Frol00/Mirage-3D-Scanning-System/software/data_processing_node/MirageApp/source/InfiniTAM-master/InfiniTAM/Apps/InfiniTAM/InfiniTAM.cpp

// Copyright 2014-2017 Oxford University Innovation Limited and the authors of InfiniTAM

#include <cstdlib>
#include <iostream>
#include <stdexcept>

#include "UIEngine.h"

#include "../../InputSource/OpenNIEngine.h"
#include "../../InputSource/Kinect2Engine.h"
#include "../../InputSource/LibUVCEngine.h"
#include "../../InputSource/PicoFlexxEngine.h"
#include "../../InputSource/RealSenseEngine.h"
#include "../../InputSource/LibUVCEngine.h"
#include "../../InputSource/RealSense2Engine.h"
#include "../../InputSource/FFMPEGReader.h"
#include "../../ITMLib/ITMLibDefines.h"
#include "../../ITMLib/Core/ITMBasicEngine.h"
#include "../../ITMLib/Core/ITMBasicSurfelEngine.h"
#include "../../ITMLib/Core/ITMMultiEngine.h"

using namespace InfiniTAM::Engine;
using namespace InputSource;
using namespace ITMLib;

/** Create a default source of depth images from a list of command line
    arguments. Typically, @para arg1 would identify the calibration file to
    use, @para arg2 the colour images, @para arg3 the depth images and
    @para arg4 the IMU images. If images are omitted, some live sources will
    be tried.
*/
static void CreateDefaultImageSource(ImageSourceEngine* & imageSource, IMUSourceEngine* & imuSource, const char *arg1, const char *arg2, const char *arg3, const char *arg4)
{
	const char *calibFile = arg1;
	const char *filename1 = arg2;
	const char *filename2 = arg3;
	const char *filename_imu = arg4;

	if (strcmp(calibFile, "viewer") == 0)
	{
		imageSource = new BlankImageGenerator("", Vector2i(640, 480));
		printf("starting in viewer mode: make sure to press n first to initiliase the views ... \n");
		return;
	}

	printf("using calibration file: %s\n", calibFile);

	if ((imageSource == NULL) && (filename2 != NULL))
	{
		printf("using rgb images: %s\nusing depth images: %s\n", filename1, filename2);
		if (filename_imu == NULL)
		{
			ImageMaskPathGenerator pathGenerator(filename1, filename2);
			imageSource = new ImageFileReader<ImageMaskPathGenerator>(calibFile, pathGenerator);
		}
		else
		{
			printf("using imu data: %s\n", filename_imu);
			imageSource = new RawFileReader(calibFile, filename1, filename2, Vector2i(320, 240), 0.5f);
			imuSource = new IMUSourceEngine(filename_imu);
		}

		if (imageSource->getDepthImageSize().x == 0)
		{
			delete imageSource;
			if (imuSource != NULL) delete imuSource;
			imuSource = NULL;
			imageSource = NULL;
		}
	}

	if ((imageSource == NULL) && (filename1 != NULL) && (filename_imu == NULL))
	{
		imageSource = new InputSource::FFMPEGReader(calibFile, filename1, filename2);
		if (imageSource->getDepthImageSize().x == 0)
		{
			delete imageSource;
			imageSource = NULL;
		}
	}

	if (imageSource == NULL)
	{
		// If no calibration file specified, use the factory default calibration
		bool useInternalCalibration = !calibFile || strlen(calibFile) == 0;

		printf("trying OpenNI device: %s - calibration: %s\n",
				filename1 ? filename1 : "<OpenNI default device>",
				useInternalCalibration ? "internal" : "from file");
		imageSource = new OpenNIEngine(calibFile, filename1, useInternalCalibration);
		if (imageSource->getDepthImageSize().x == 0)
		{
			delete imageSource;
			imageSource = NULL;
		}
	}

	if (imageSource == NULL)
	{
		printf("trying UVC device\n");
		imageSource = new LibUVCEngine(calibFile);
		if (imageSource->getDepthImageSize().x == 0)
		{
			delete imageSource;
			imageSource = NULL;
		}
	}

	if (imageSource == NULL)
	{
		printf("trying RealSense device\n");
		imageSource = new RealSenseEngine(calibFile);
		if (imageSource->getDepthImageSize().x == 0)
		{
			delete imageSource;
			imageSource = NULL;
		}
	}

    if (imageSource == NULL)
    {
        printf("trying RealSense device with SDK 2.X (librealsense2)\n");
        imageSource = new RealSense2Engine(calibFile);
        if (imageSource->getDepthImageSize().x == 0)
        {
            delete imageSource;
            imageSource = NULL;
        }
    }

    if (imageSource == NULL)
	{
		printf("trying MS Kinect 2 device\n");
		imageSource = new Kinect2Engine(calibFile);
		if (imageSource->getDepthImageSize().x == 0)
		{
			delete imageSource;
			imageSource = NULL;
		}
	}

	if (imageSource == NULL)
	{
		printf("trying PMD PicoFlexx device\n");
		imageSource = new PicoFlexxEngine(calibFile);
		if (imageSource->getDepthImageSize().x == 0)
		{
			delete imageSource;
			imageSource = NULL;
		}
	}
}

static ITMMainEngine *CreateMainEngine(const ITMLibSettings *internalSettings, ImageSourceEngine *imageSource)
{
	switch (internalSettings->libMode)
	{
	case ITMLibSettings::LIBMODE_BASIC:
		return new ITMBasicEngine<ITMVoxel, ITMVoxelIndex>(internalSettings, imageSource->getCalib(), imageSource->getRGBImageSize(), imageSource->getDepthImageSize());
	case ITMLibSettings::LIBMODE_BASIC_SURFELS:
		return new ITMBasicSurfelEngine<ITMSurfelT>(internalSettings, imageSource->getCalib(), imageSource->getRGBImageSize(), imageSource->getDepthImageSize());
	case ITMLibSettings::LIBMODE_LOOPCLOSURE:
		return new ITMMultiEngine<ITMVoxel, ITMVoxelIndex>(internalSettings, imageSource->getCalib(), imageSource->getRGBImageSize(), imageSource->getDepthImageSize());
	default:
		throw std::runtime_error("Unsupported library mode!");
	}
}

int main(int argc, char** argv)
try
{
	const char *arg1 = "";
	const char *arg2 = NULL;
	const char *arg3 = NULL;
	const char *arg4 = NULL;

	int arg = 1;
	do {
		if (argv[arg] != NULL) arg1 = argv[arg]; else break;
		++arg;
		if (argv[arg] != NULL) arg2 = argv[arg]; else break;
		++arg;
		if (argv[arg] != NULL) arg3 = argv[arg]; else break;
		++arg;
		if (argv[arg] != NULL) arg4 = argv[arg]; else break;
	} while (false);

	if (arg == 1) {
		printf("usage: %s [<calibfile> [<imagesource>] ]\n"
		       "  <calibfile>   : path to a file containing intrinsic calibration parameters\n"
		       "  <imagesource> : either one argument to specify OpenNI device ID\n"
		       "                  or two arguments specifying rgb and depth file masks\n"
		       "\n"
		       "examples:\n"
		       "  %s ./Files/Teddy/calib.txt ./Files/Teddy/Frames/%%04i.ppm ./Files/Teddy/Frames/%%04i.pgm\n"
		       "  %s ./Files/Teddy/calib.txt\n\n", argv[0], argv[0], argv[0]);
	}

	printf("initialising ...\n");
	ImageSourceEngine *imageSource = NULL;
	IMUSourceEngine *imuSource = NULL;

	if (arg == 1)
	{
		printf("starting D415 GUI mode. Use Apply & Initialize Camera in the left panel.\n");
		imageSource = new BlankImageGenerator(arg1, Vector2i(848, 480));
	}
	else
	{
		CreateDefaultImageSource(imageSource, imuSource, arg1, arg2, arg3, arg4);
	}

	if (imageSource==NULL)
	{
		std::cout << "failed to open any image stream" << std::endl;
		return -1;
	}

	ITMLibSettings *internalSettings = new ITMLibSettings();

	ITMMainEngine *mainEngine = CreateMainEngine(internalSettings, imageSource);

	UIEngine::Instance()->Initialise(argc, argv, imageSource, imuSource, mainEngine, "./Files/Out", internalSettings, arg1);
	UIEngine::Instance()->Run();
	UIEngine::Instance()->Shutdown();

	delete internalSettings;
	return 0;
}
catch(std::exception& e)
{
	std::cerr << e.what() << '\n';
	return EXIT_FAILURE;
}
